huytd/snackymini-keyboard/firmware/metadata.c

#include "usb_names.h"

#define MANUFACTURER_NAME     {'S','n','a','c','k','y'}
#define MANUFACTURER_NAME_LEN 6
#define PRODUCT_NAME          {'S','n','a','c','k','y','M','i','n','i'}
#define PRODUCT_NAME_LEN      10

struct usb_string_descriptor_struct usb_string_manufacturer_name = {
  2 + MANUFACTURER_NAME_LEN * 2,
  3,
  MANUFACTURER_NAME
};

struct usb_string_descriptor_struct usb_string_product_name = {
  2 + PRODUCT_NAME_LEN * 2,
  3,
  PRODUCT_NAME
};
